maciejmiklas/resistative-plant-monitor/PlantMonitor.h

#ifndef FlowerMonitor_H_
#define FlowerMonitor_H_

#include <Arduino.h>
#include "Timer.h"
#include "Lcd.h"
#include "MoistureMeter.h"
#include "Sos.h"
#include "Log.h"
#include "Alarm.h"

#ifdef __cplusplus
extern "C" {
#endif
void loop();
void setup();
#ifdef __cplusplus
} // extern "C"
#endif

#endif /* FlowerMonitor_H_ */
